antmicro/hdmi-mipi-bridge/assets/previews/layer1.png

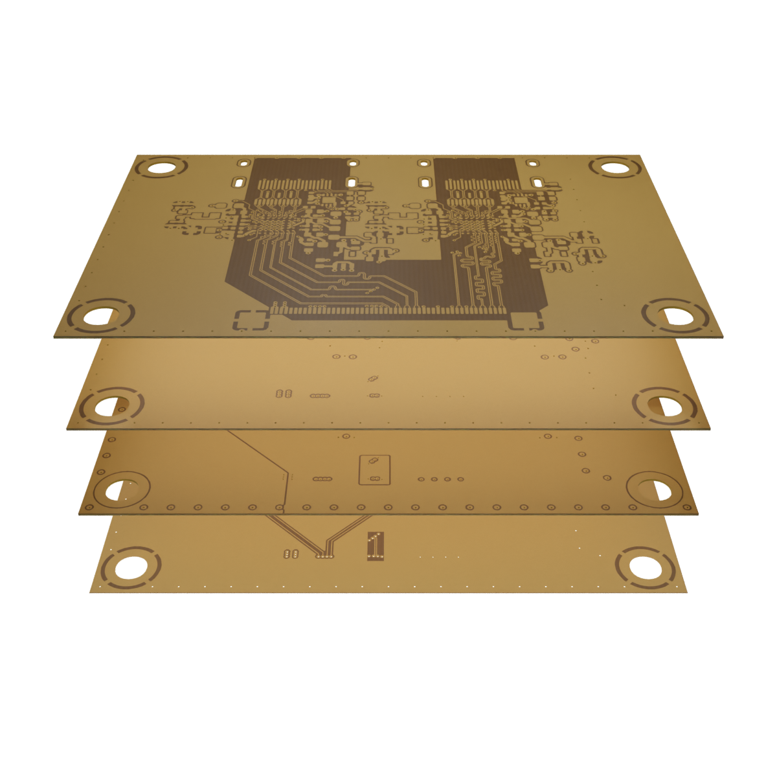
assets/previews/layer1.png
