antmicro/hdmi-mipi-bridge/assets/previews/layer4.png

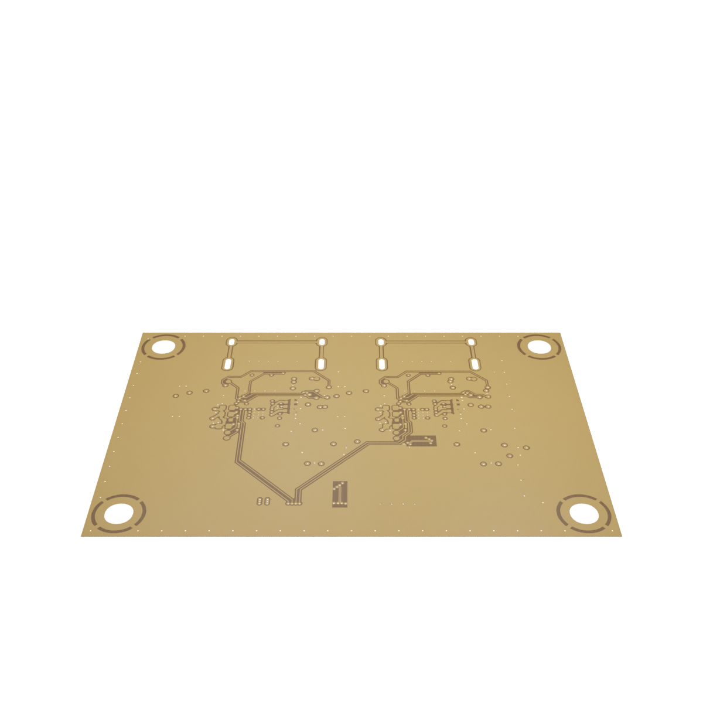
assets/previews/layer4.png
