antmicro/hdmi-mipi-bridge/assets/previews/leftT.png

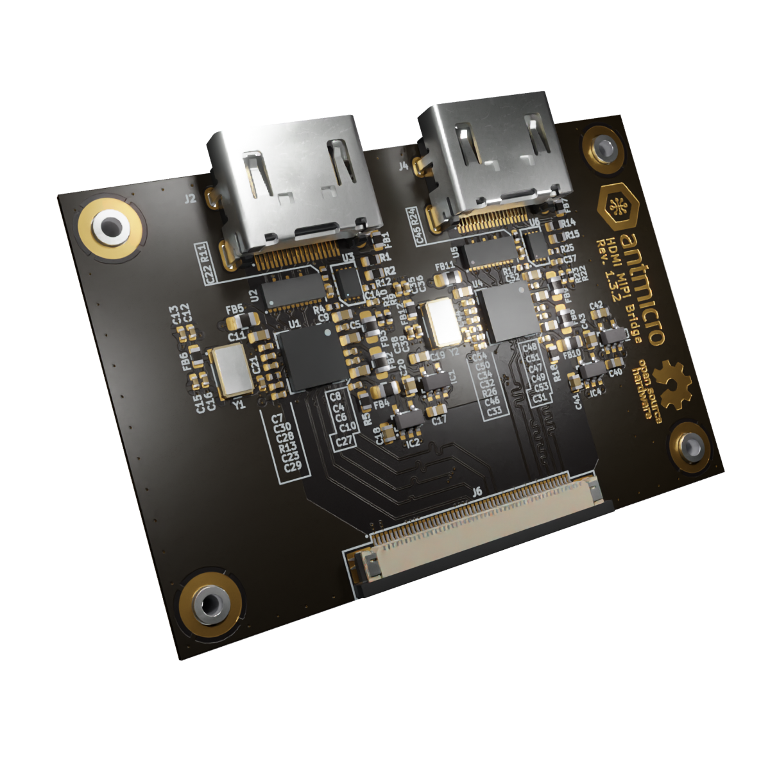
assets/previews/leftT.png
