antmicro/hdmi-mipi-bridge/assets/previews/orthoB.png

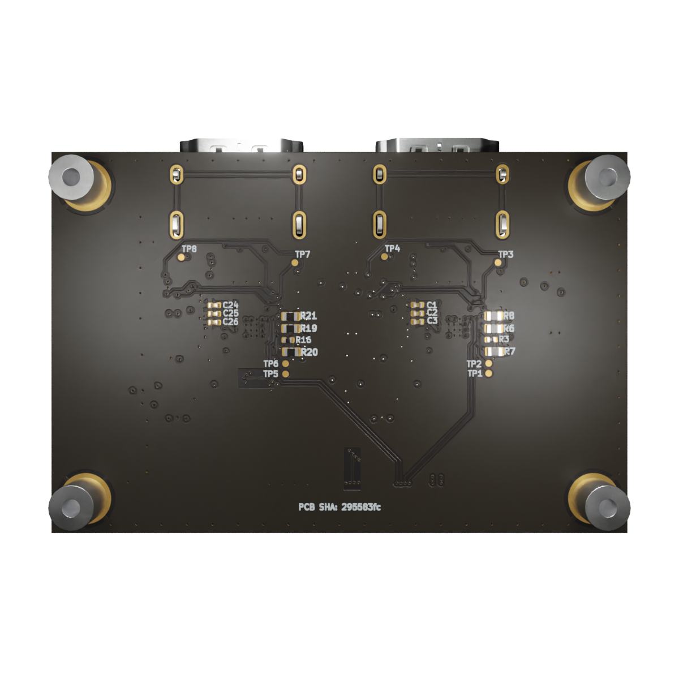
assets/previews/orthoB.png
