antmicro/hdmi-mipi-bridge/assets/previews/orthoT.png

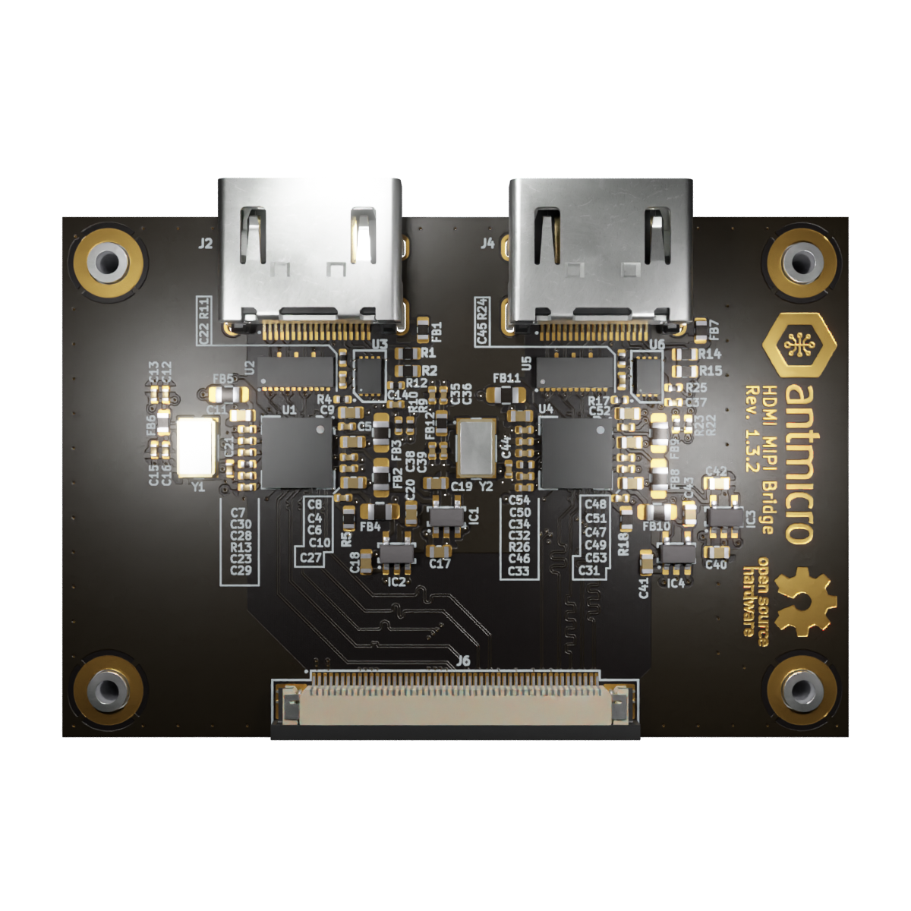
assets/previews/orthoT.png
