antmicro/hdmi-mipi-bridge/assets/previews/rightB.png

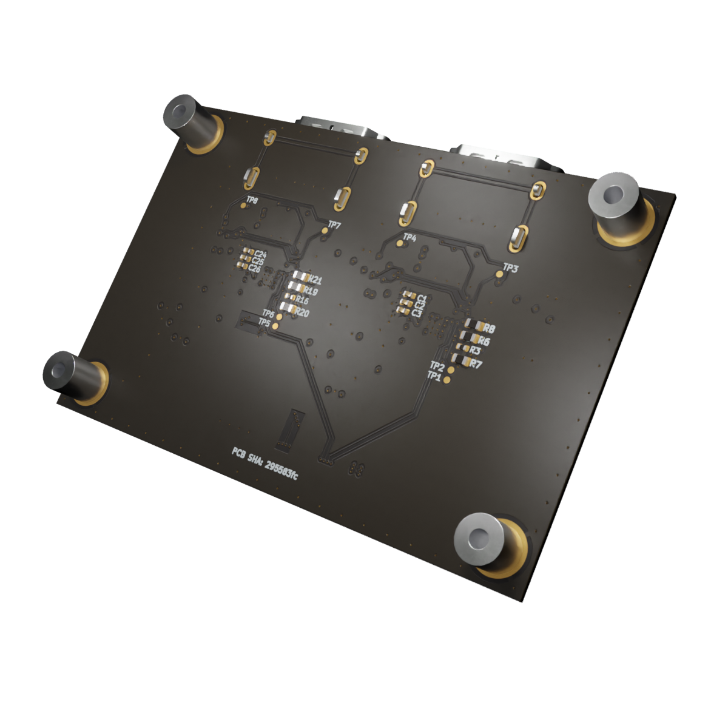
assets/previews/rightB.png
